Bojtronic/Horno_DGC/IMAGENES/Step down 2.jpeg

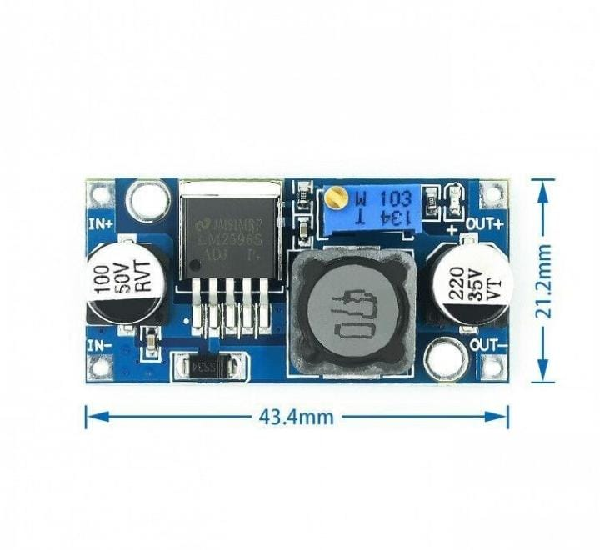
IMAGENES/Step down 2.jpeg
