Bojtronic/Horno_DGC/IMAGENES/PCB pistas.png

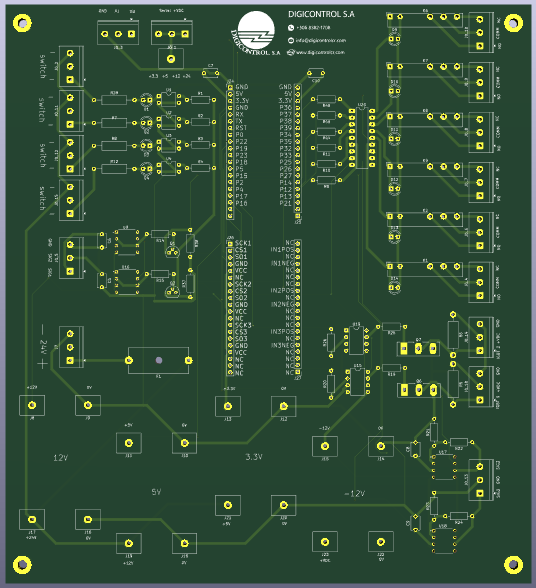
IMAGENES/PCB pistas.png
