Bojtronic/Horno_DGC/IMAGENES/UART USB.jpg

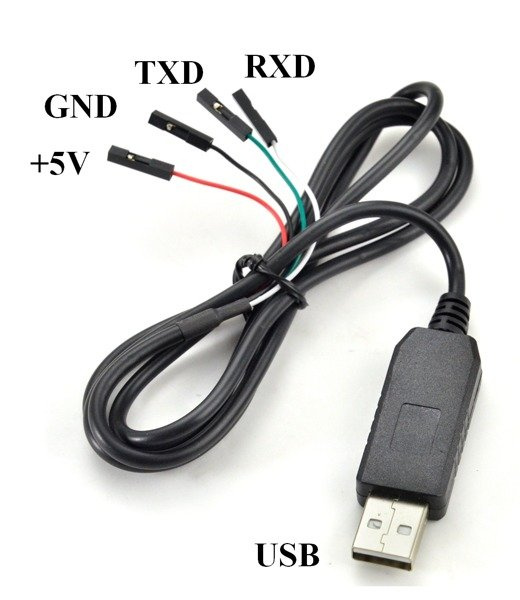
IMAGENES/UART USB.jpg
