Bojtronic/Horno_DGC/IMAGENES/PCB componentes.png

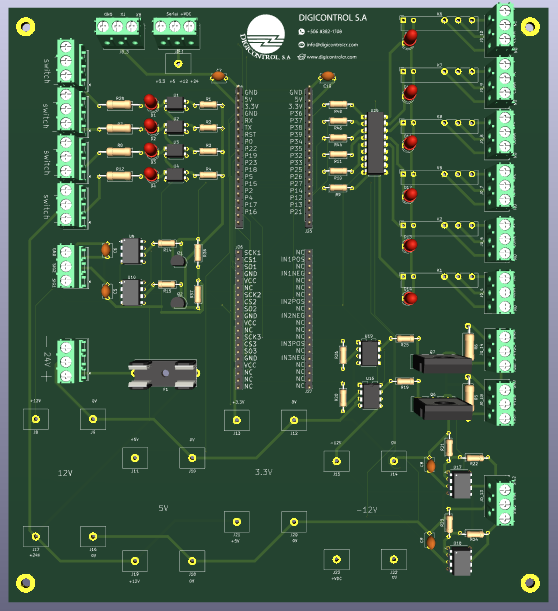
IMAGENES/PCB componentes.png
