Bojtronic/Horno_DGC/CODIGO/HORNO_ESP32/test_entradas.h

#ifndef TEST_ENTRADAS_H
#define TEST_ENTRADAS_H

#include <Arduino.h>
#include "config.h"

// Inicializa la prueba de entradas
void testEntradasInit();

// Ejecuta continuamente la prueba de entradas
void testEntradasUpdate();

#endif
