Bojtronic/Horno_DGC/CODIGO/HORNO_ESP32/test_salidas.h

#ifndef TEST_SALIDAS_H
#define TEST_SALIDAS_H

#include <Arduino.h>
#include "config.h"

// Inicializa la prueba de salidas
void testSalidasInit();

// Ejecuta continuamente la secuencia de salidas
void testSalidasUpdate();

#endif
